PierceATronics/T2_Buzzinator/LTSpice_Simulation/Programmable_Timed_Buzzer_Sim.asc

C1: cap; 0.1µ
C2: cap; 0.1µ
C3: cap; 10µ
C4: cap; 0.1µ
D1: diode; 1N4148
L1: ind; 1µ
M1: nmos; 2N7002
Push_Button: voltage; PULSE(9 0 0.05 0 0 0.01 0 1)
R1: res; 3k
R2: res; 130
R3: res; 100k
R4: res; 100k
R5: res; 100
U1: NE555
U2: NE555
VCC: voltage; 9
Named nets: 0, 9V, PB, TP1, TP2
.tran 2
CEM-1212S MAGNETIC BUZZER MODEL
555 TIMER 2
ASTABLE MODE 
(50% DUTY CYCLE SQUARE-WAVE)
F0=2400HZ
555 TIMER 1
MONOSTABLE MODE
SINGLE PULSE GENERATION
SIMULATE TACTILE PUSH BUTTON
BUTTON IS PRESSED AT T=0.05S
BUTTON IS HELD DOWN FOR T=0.01S
WHEN THE PUSH BUTTON IS PRESSED, A SINGLE PULSE OF DURATION T=1.1*R3*C3 
WILL BE GENERATED. THIS CAN BE MEASURED AT TP1. THE PULSE WILL 
ENABLE 555 TIMER 2 TO GENERATE A 2.4KHZ SQUARE-WAVE SIGNAL FOR 
THE DURATION.
